nikhilmurty/robot-hand/hardware/IMG_2483.jpeg

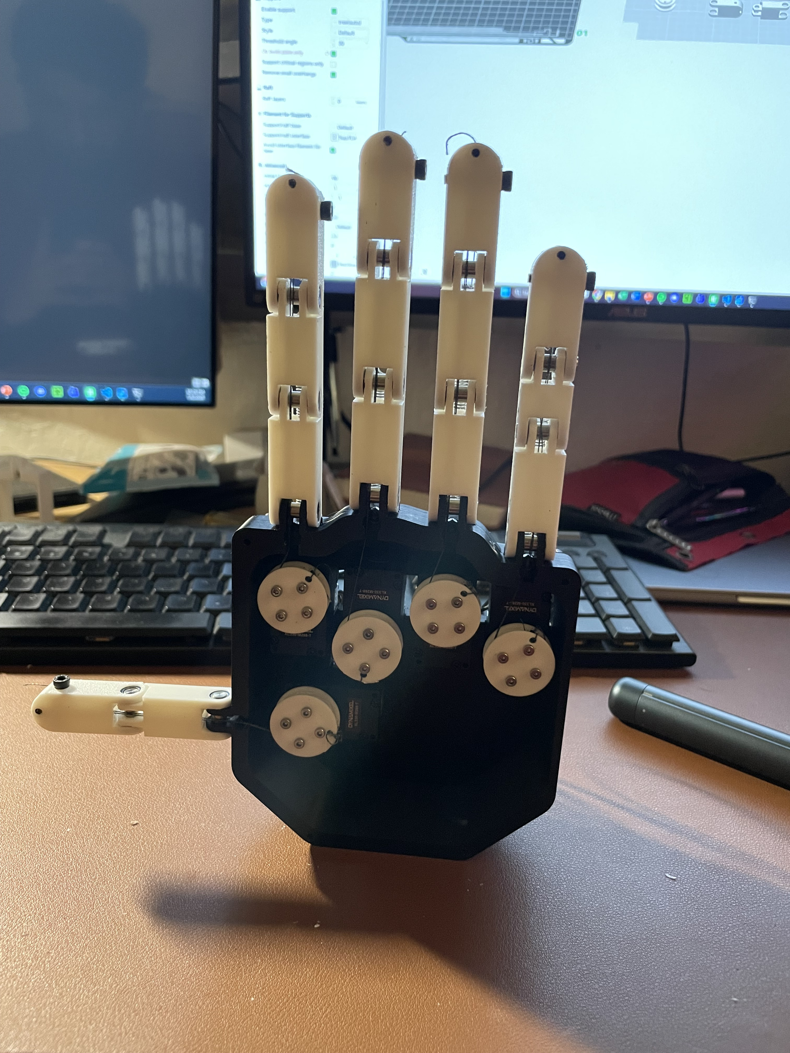
hardware/IMG_2483.jpeg
